RCMgames/RCM_hardware_documentation_and_user_guide/Robot Control Module/V3/circuit diagram and fritzing design/images/image (2).png

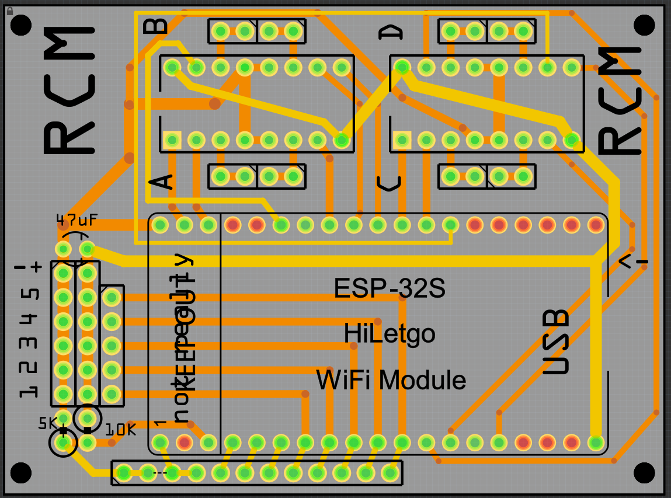
Robot Control Module/V3/circuit diagram and fritzing design/images/image (2).png
